LilianChagnaud/VarroaProjectELEC4/01 - Données d'entrée/Comptage-de-Varroa-main/Images/Capture d’écran 2025-04-26 à 15.22.17.png

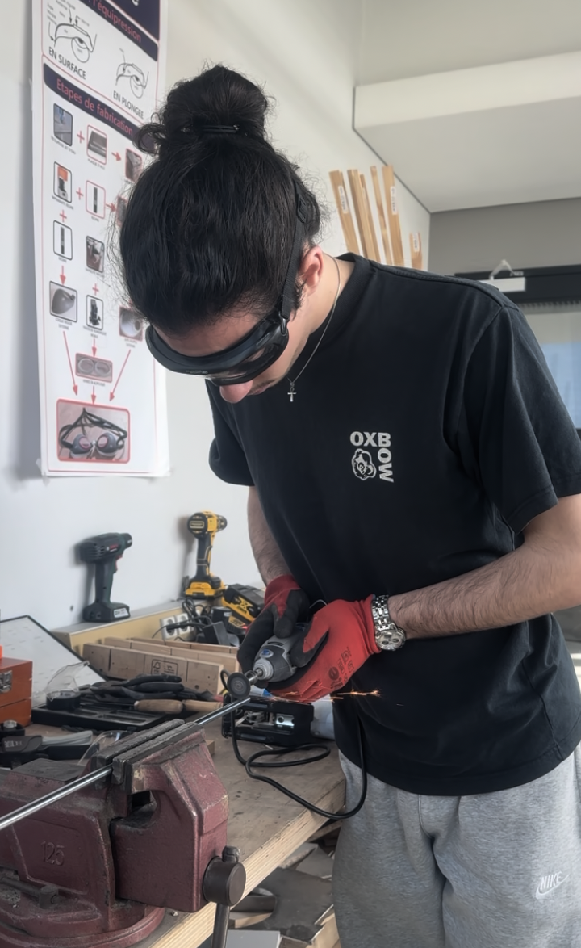
01 - Données d'entrée/Comptage-de-Varroa-main/Images/Capture d’écran 2025-04-26 à 15.22.17.png
