LilianChagnaud/VarroaProjectELEC4/01 - Données d'entrée/Comptage-de-Varroa-main/Images/Capture d’écran 2024-12-08 à 14.12.38.png

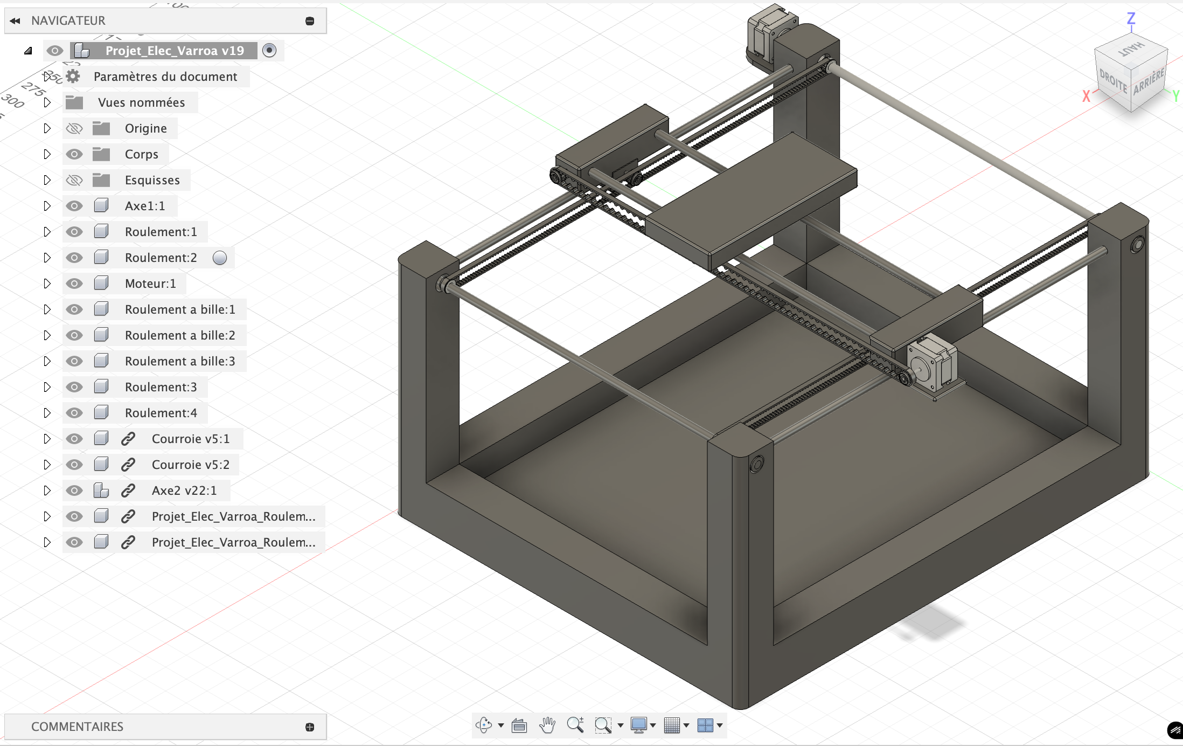
01 - Données d'entrée/Comptage-de-Varroa-main/Images/Capture d’écran 2024-12-08 à 14.12.38.png
