LilianChagnaud/VarroaProjectELEC4/01 - Données d'entrée/Comptage-de-Varroa-main/Images/Capture d’écran 2024-12-09 à 11.55.22.png

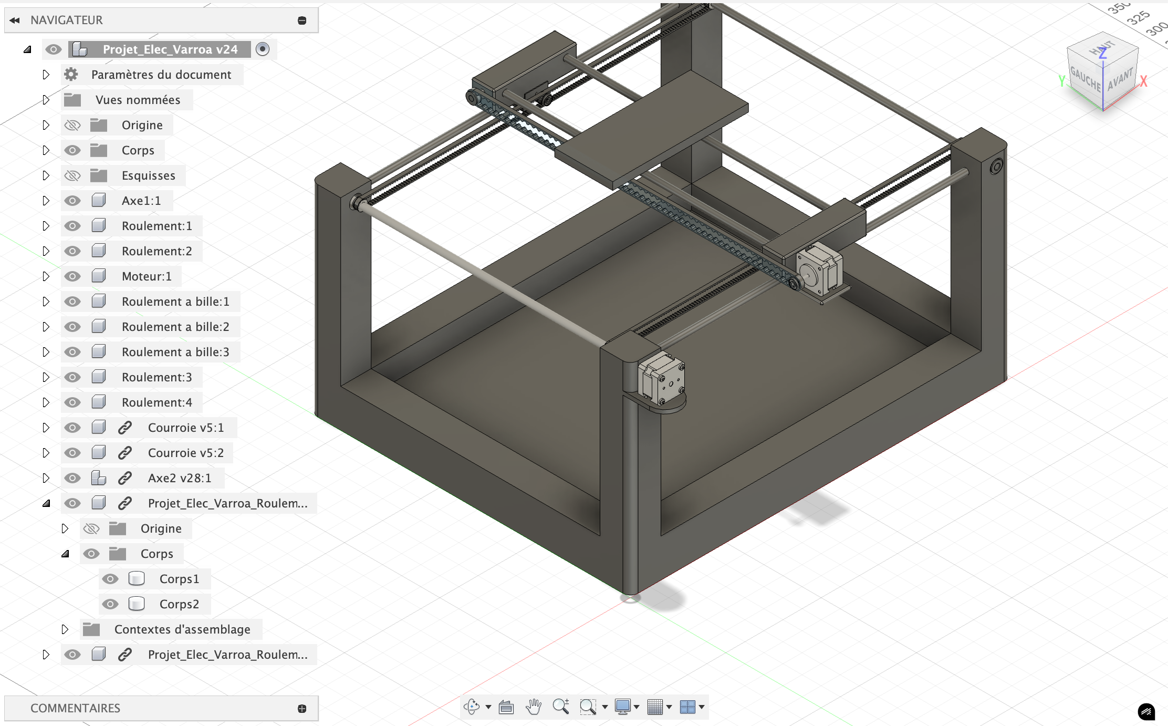
01 - Données d'entrée/Comptage-de-Varroa-main/Images/Capture d’écran 2024-12-09 à 11.55.22.png
