LilianChagnaud/VarroaProjectELEC4/01 - Données d'entrée/Comptage-de-Varroa-main/Images/Capture d’écran 2024-12-09 à 15.05.34.png

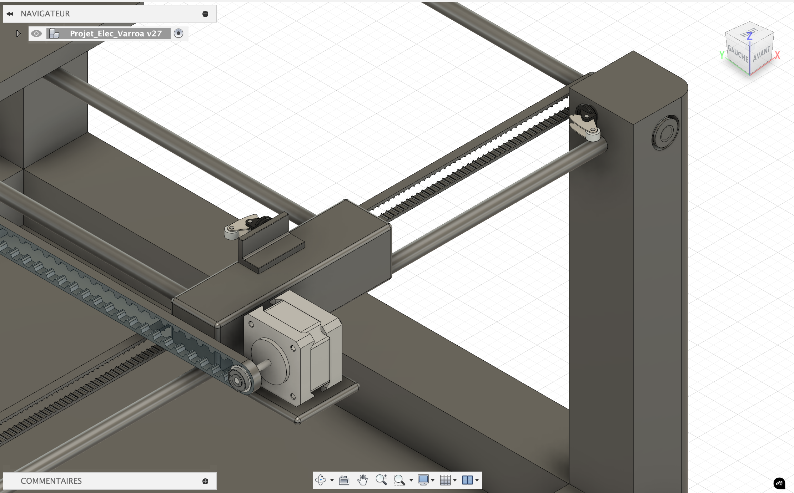
01 - Données d'entrée/Comptage-de-Varroa-main/Images/Capture d’écran 2024-12-09 à 15.05.34.png
