LilianChagnaud/VarroaProjectELEC4/01 - Données d'entrée/Comptage-de-Varroa-main/Test_Wifi.ino

#include <WiFi.h>

const char* ssid = "Redmi Note 10 5G";
const char* password = "3ee7230b";

void setup() {
  Serial.begin(115200);
  WiFi.begin(ssid, password);
  Serial.println("Connexion en cours...");

  while (WiFi.status() != WL_CONNECTED) {
    delay(1000);
    Serial.print(".");
  }

  Serial.println("\nConnecté !");
  Serial.print("Adresse IP : ");
  Serial.println(WiFi.localIP());
}

void loop() {
}
